smeisner/smart-thermostat/app/include/aht.h

/*
 * Copyright (c) 2021 Ruslan V. Uss <unclerus@gmail.com>
 *
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
 * THIS SOFTWARE IS PROVIDED BY THE COPYRIGHT HOLDERS AND CONTRIBUTORS "AS IS"
 * AND ANY EXPRESS OR IMPLIED WARRANTIES, INCLUDING, BUT NOT LIMITED TO, THE
 * IMPLIED WARRANTIES OF MERCHANTABILITY AND FITNESS FOR A PARTICULAR PURPOSE ARE
 * DISCLAIMED. IN NO EVENT SHALL THE COPYRIGHT HOLDER OR CONTRIBUTORS BE LIABLE
 * FOR ANY DIRECT, INDIRECT, INCIDENTAL, SPECIAL, EXEMPLARY, OR CONSEQUENTIAL
 * DAMAGES (INCLUDING, BUT NOT LIMITED TO, PROCUREMENT OF SUBSTITUTE GOODS OR
 * SERVICES; LOSS OF USE, DATA, OR PROFITS; OR BUSINESS INTERRUPTION) HOWEVER
 * CAUSED AND ON ANY THEORY OF LIABILITY, WHETHER IN CONTRACT, STRICT LIABILITY,
 * OR TORT (INCLUDING NEGLIGENCE OR OTHERWISE) ARISING IN ANY WAY OUT OF THE USE
 * OF THIS SOFTWARE, EVEN IF ADVISED OF THE POSSIBILITY OF SUCH DAMAGE.
 */

/**
 * @file aht.h
 * @defgroup aht aht
 * @{
 *
 * ESP-IDF driver for humidty/temperature sensors AHT10/AHT15/AHT20
 *
 * Copyright (c) 2021 Ruslan V. Uss <unclerus@gmail.com>
 *
 * BSD Licensed as described in the file LICENSE
 */
#ifndef __AHT_H__
#define __AHT_H__

#define HELPER_TARGET_IS_ESP32 1

#include <i2cdev.h>
#include <stdbool.h>

#define AHT_I2C_ADDRESS_GND 0x38 //!< Device address when ADDR pin connected to GND
#define AHT_I2C_ADDRESS_VCC 0x39 //!< Device address when ADDR pin connected to VCC

#ifdef __cplusplus
extern "C" {
#endif

/**
 * Device types
 */
typedef enum {
    AHT_TYPE_AHT1x = 0, //!< AHT10, AHT15
    AHT_TYPE_AHT20,     //!< AHT20
} aht_type_t;

/**
 * Device modes
 */
typedef enum {
    AHT_MODE_NORMAL = 0, //!< Normal mode
    AHT_MODE_CYCLE,      //!< Continuous measurements mode, undocumented
} aht_mode_t;

/**
 * Device descriptor
 */
typedef struct
{
    i2c_dev_t i2c_dev;
    aht_type_t type;
    aht_mode_t mode;
} aht_t;

/**
 * @brief Initialize device descriptor
 *
 * @param dev      Device descriptor
 * @param addr     Device I2C address
 * @param port     I2C port
 * @param sda_gpio SDA GPIO
 * @param scl_gpio SCL GPIO
 * @return `ESP_OK` on success
 */
esp_err_t aht_init_desc(aht_t *dev, uint8_t addr, i2c_port_t port, gpio_num_t sda_gpio, gpio_num_t scl_gpio);

/**
 * @brief Free device descriptor
 *
 * @param dev Device descriptor
 * @return `ESP_OK` on success
 */
esp_err_t aht_free_desc(aht_t *dev);

/**
 * @brief Init device
 *
 * @param dev Device descriptor
 * @return `ESP_OK` on success
 */
esp_err_t aht_init(aht_t *dev);

/**
 * @brief Soft reset device
 *
 * @param dev Device descriptor
 * @return `ESP_OK` on success
 */
esp_err_t aht_reset(aht_t *dev);

/**
 * @brief Get device status
 *
 * @param dev Device descriptor
 * @param[out] busy       Busy flag
 *                        - true: device currently measuring
 *                        - false: device in indle mode
 * @param[out] calibrated Calibration success flag
 *                        - true: sensor calibrated
 *                        - false: sensor not calibrated
 * @return `ESP_OK` on success
 */
esp_err_t aht_get_status(aht_t *dev, bool *busy, bool *calibrated);

/**
 * @brief Get temperature and relative humidity
 *
 * @param dev Device descriptor
 * @param[out] temperature Temperature, degrees Celsius
 * @param[out] humidity    Relative humidity, percents
 * @return `ESP_OK` on success
 */
esp_err_t aht_get_data(aht_t *dev, float *temperature, float *humidity);

#ifdef __cplusplus
}
#endif

/**@}*/

#endif /* __AHT_H__ */
