smeisner/smart-thermostat/app/src/Thermostat_events.py

def tftAwaken(event_struct):
    return


def tftHvacModeChange(event_struct):
    return


def tftBeep(event_struct):
    return


def tftStopTouchTimer(event_struct):
    return


def tftUpdateTempSet(event_struct):
    return


def tftDecreaseSetTemp(event_struct):
    return


def tftIncreaseSetTemp(event_struct):
    return


def LoadInfoStrings(event_struct):
    return


def LoadConfigSettings(event_struct):
    return


def tftUpdateTempCorrectionValue(event_struct):
    return


def tftUpdateTempSwingValue(event_struct):
    return


def LoadUncommonSettings(event_struct):
    return


def SaveConfigSettings(event_struct):
    return


def tftCalibrate(event_struct):
    return


def tftUpdateUiSleepValue(event_struct):
    return


def tftClearPsk(event_struct):
    return


def SaveUncommonConfigSettings(event_struct):
    return


def StartWifiScan(event_struct):
    return


def tftSetNewWifi(event_struct):
    return


def stopWifiScan(event_struct):
    return


def ShowQrOnScreen(event_struct):
    return


def tftCountdown(event_struct):
    return
